pasztorpisti/flashforge-adventurer-3-lid/img/NF-A9x14.png

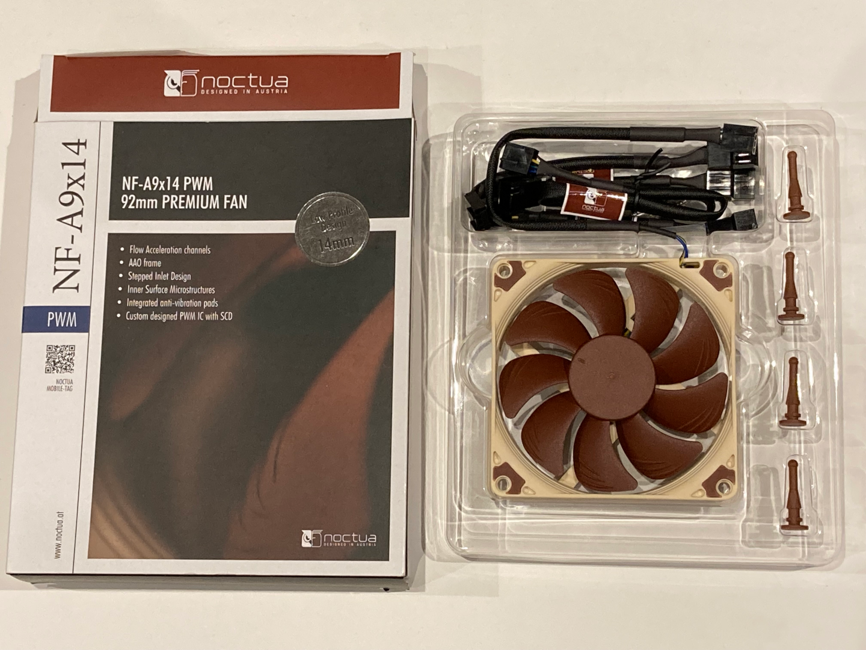
img/NF-A9x14.png
