pasztorpisti/flashforge-adventurer-3-lid/img/NF-A9x14_lid.png

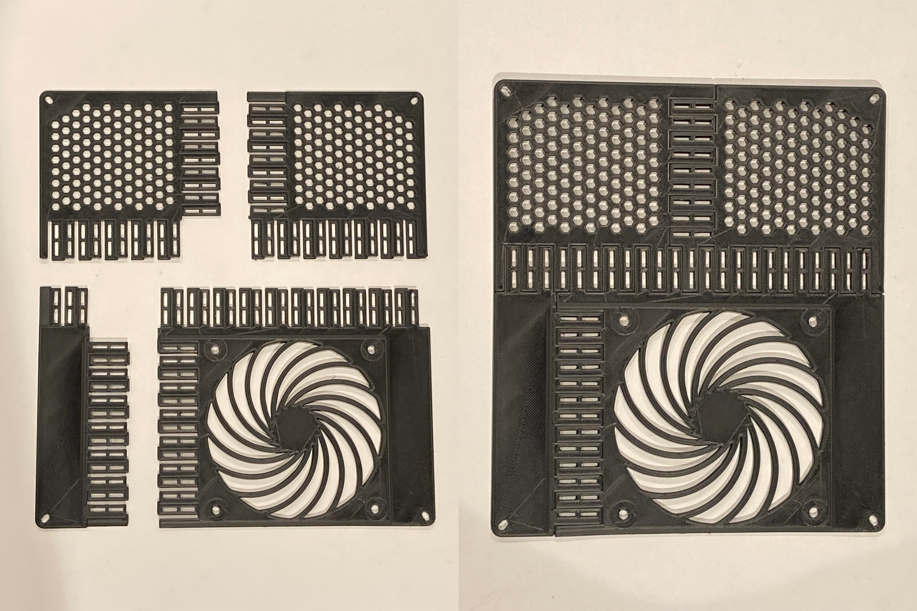
img/NF-A9x14_lid.png
