pasztorpisti/flashforge-adventurer-3-lid/img/NF-A9x14_running.png

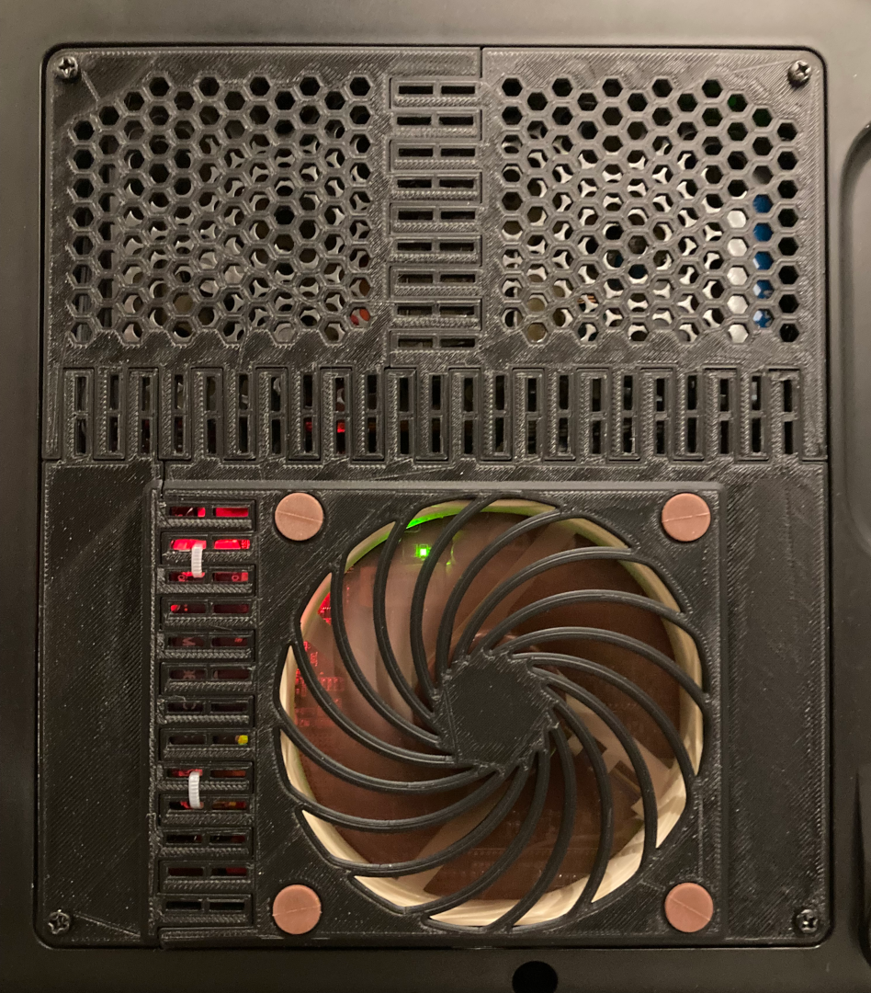
img/NF-A9x14_running.png
