pasztorpisti/flashforge-adventurer-3-lid/img/NF-A9x14_with_buck_converter.png

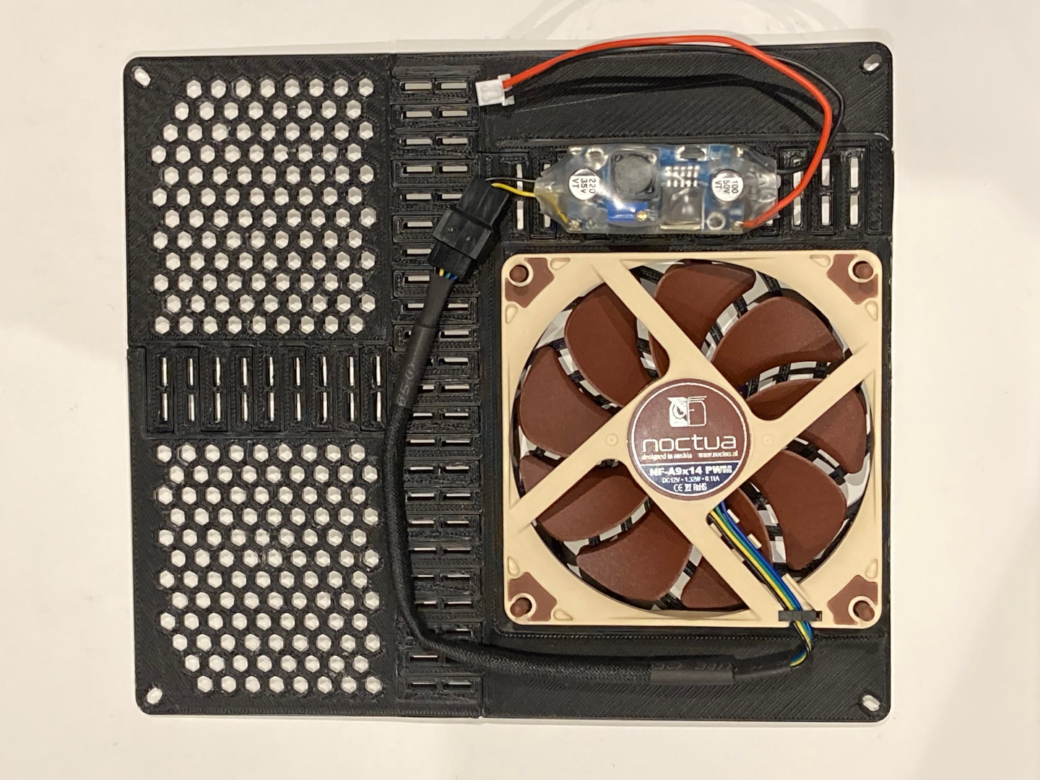
img/NF-A9x14_with_buck_converter.png
