pasztorpisti/flashforge-adventurer-3-lid/stl/lid-92mm/0.18z_0.20xy_lid_top_right.stl

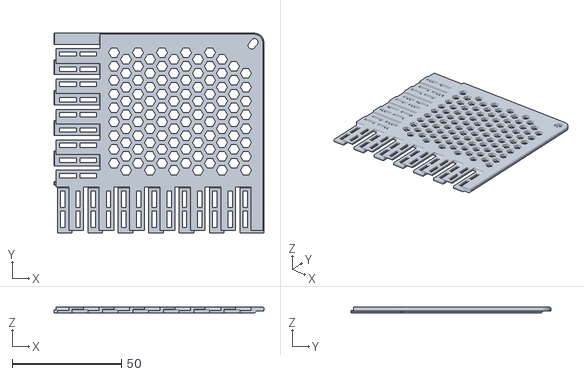
[picture p23: CAD file, 2024-04-19]
stl/lid-92mm/0.18z_0.20xy_lid_top_right.stl
96.0 x 91.3 x 2.88
