pasztorpisti/flashforge-adventurer-3-lid/stl/lid-92mm/0.36z_0.35xy_lid_bottom_left_raised.stl

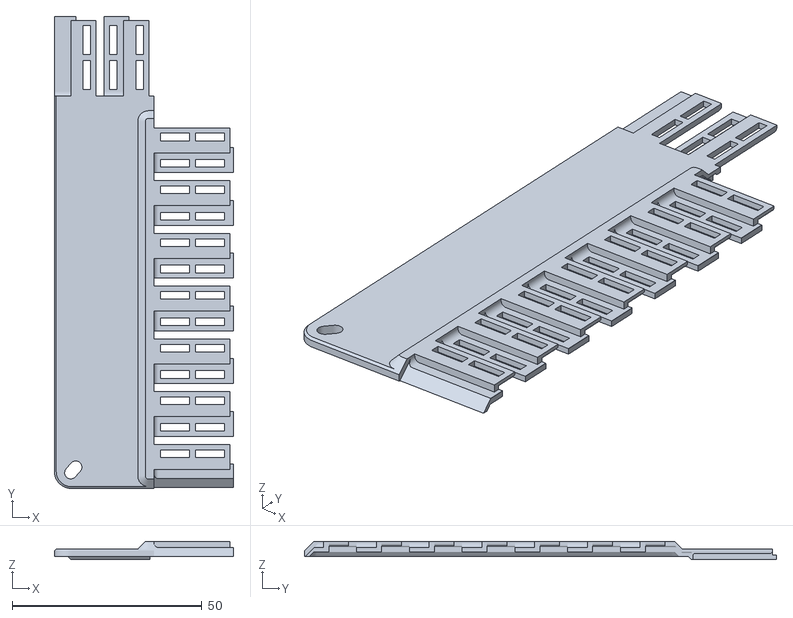
[picture p24: CAD file, 2024-04-19]
stl/lid-92mm/0.36z_0.35xy_lid_bottom_left_raised.stl
47.2 x 124.3 x 4.86
