pasztorpisti/flashforge-adventurer-3-lid/stl/lid-single-part/lid_2x40mm_fans.stl

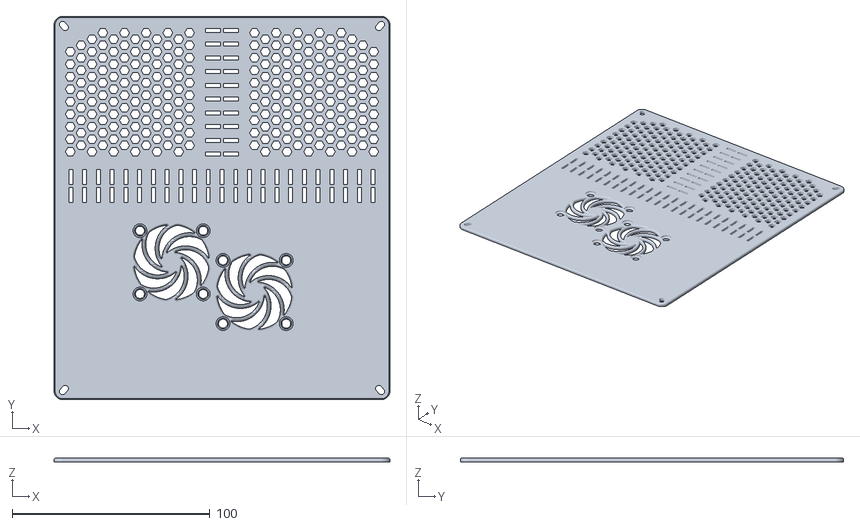
[picture p25: CAD file, 2024-04-19]
stl/lid-single-part/lid_2x40mm_fans.stl
170.0 x 194.0 x 2.00
