pasztorpisti/flashforge-adventurer-3-lid/stl/lid-40mm_or_80mm/0.18z_0.35xy_lid_bottom_left_80mm_fan.stl

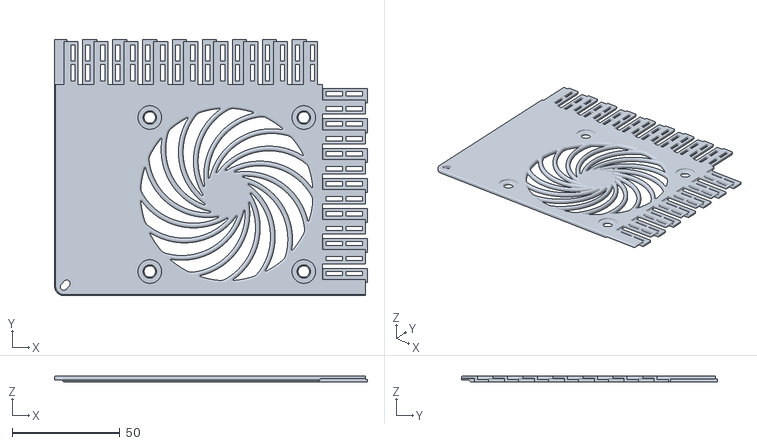
[picture p26: CAD file, 2024-04-19]
stl/lid-40mm_or_80mm/0.18z_0.35xy_lid_bottom_left_80mm_fan.stl
145.3 x 119.1 x 2.88
