pasztorpisti/flashforge-adventurer-3-lid/stl/lid-92mm/0.18z_0.35xy_lid_bottom_left_flat.stl

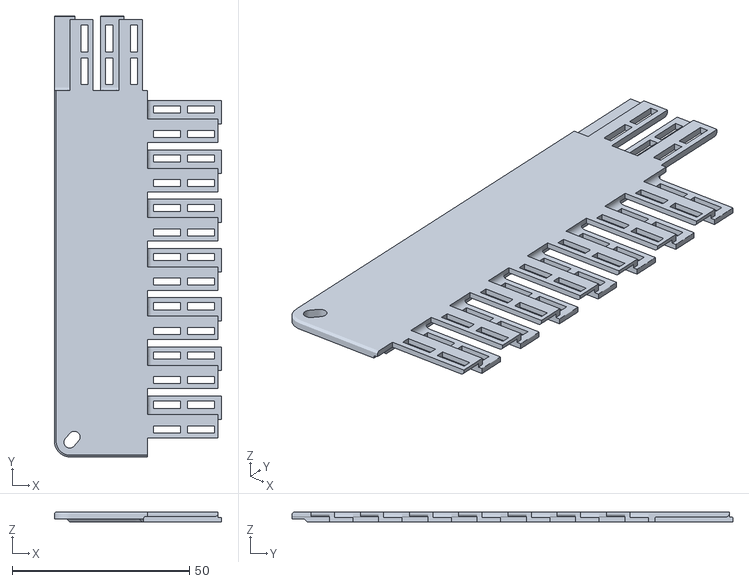
[picture p27: CAD file, 2024-04-19]
stl/lid-92mm/0.18z_0.35xy_lid_bottom_left_flat.stl
47.2 x 124.5 x 2.88
