pasztorpisti/flashforge-adventurer-3-lid/stl/lid-40mm_or_80mm/0.18z_0.30xy_lid_bottom_right.stl

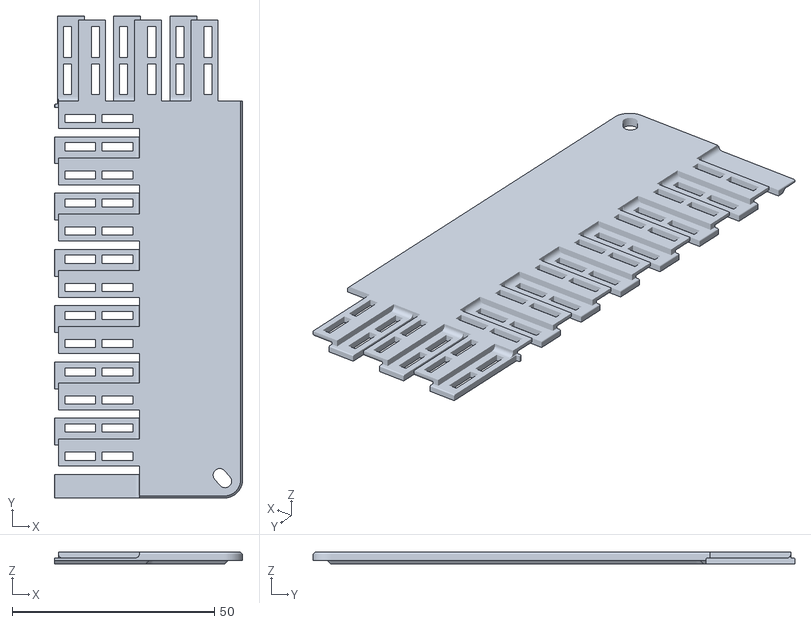
[picture p28: CAD file, 2024-04-19]
stl/lid-40mm_or_80mm/0.18z_0.30xy_lid_bottom_right.stl
46.5 x 119.1 x 2.88
