pasztorpisti/flashforge-adventurer-3-lid/stl/lid-40mm_or_80mm/0.36z_0.25xy_lid_bottom_right.stl

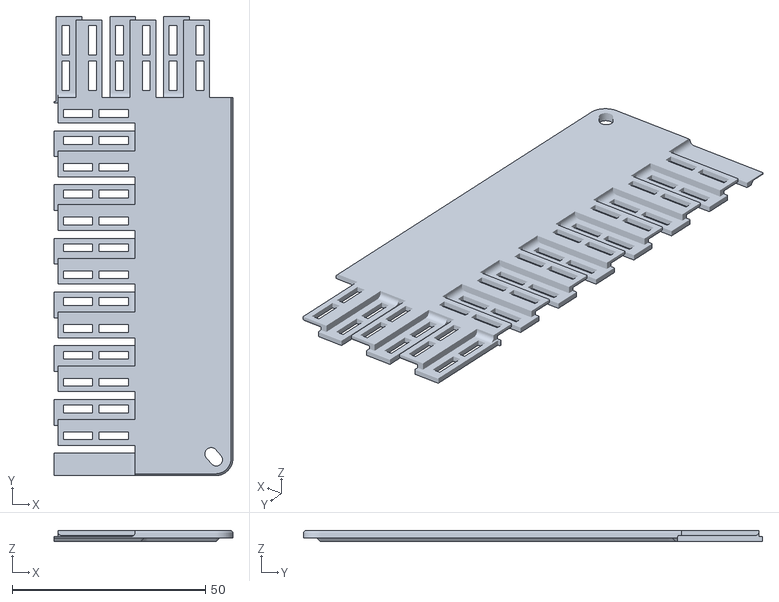
[picture p29: CAD file, 2024-04-19]
stl/lid-40mm_or_80mm/0.36z_0.25xy_lid_bottom_right.stl
46.3 x 118.9 x 2.88
