pasztorpisti/flashforge-adventurer-3-lid/stl/lid-92mm/0.36z_0.15xy_lid_bottom_right_flat.stl

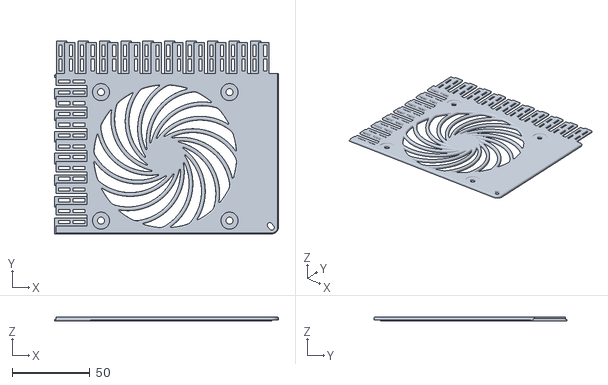
[picture p30: CAD file, 2024-04-19]
stl/lid-92mm/0.36z_0.15xy_lid_bottom_right_flat.stl
144.4 x 124.3 x 2.88
