pasztorpisti/flashforge-adventurer-3-lid/stl/lid-92mm/0.18z_0.25xy_lid_bottom_right_flat.stl

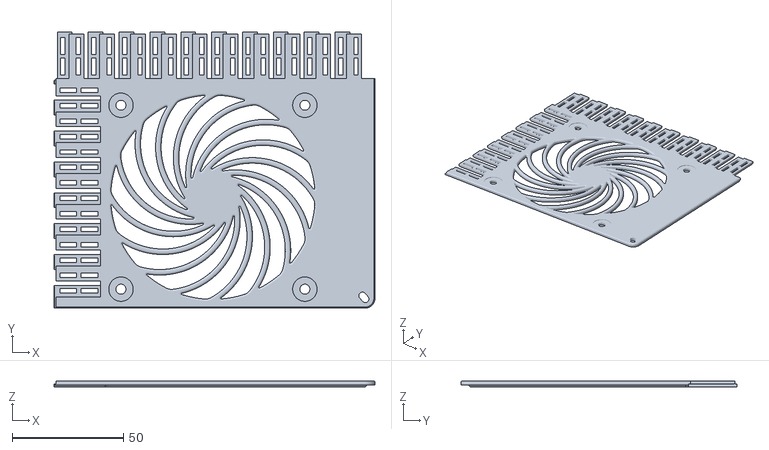
[picture p31: CAD file, 2024-04-19]
stl/lid-92mm/0.18z_0.25xy_lid_bottom_right_flat.stl
144.6 x 124.5 x 2.88
