pasztorpisti/flashforge-adventurer-3-lid/stl/lid-40mm_or_80mm/0.18z_0.20xy_lid_bottom_left_40mm_fans.stl

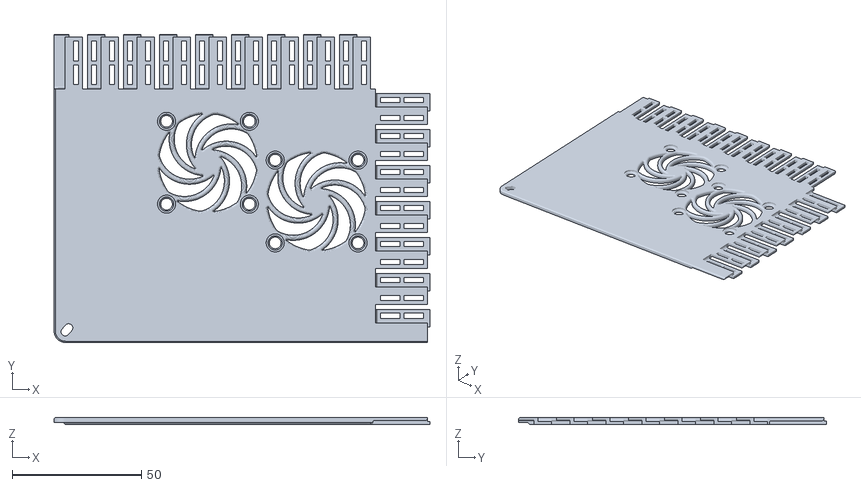
[picture p32: CAD file, 2024-04-19]
stl/lid-40mm_or_80mm/0.18z_0.20xy_lid_bottom_left_40mm_fans.stl
145.3 x 119.1 x 2.88
