pasztorpisti/flashforge-adventurer-3-lid/img/NF-A4x20_and_NF-A4x10_fully_assembled.png

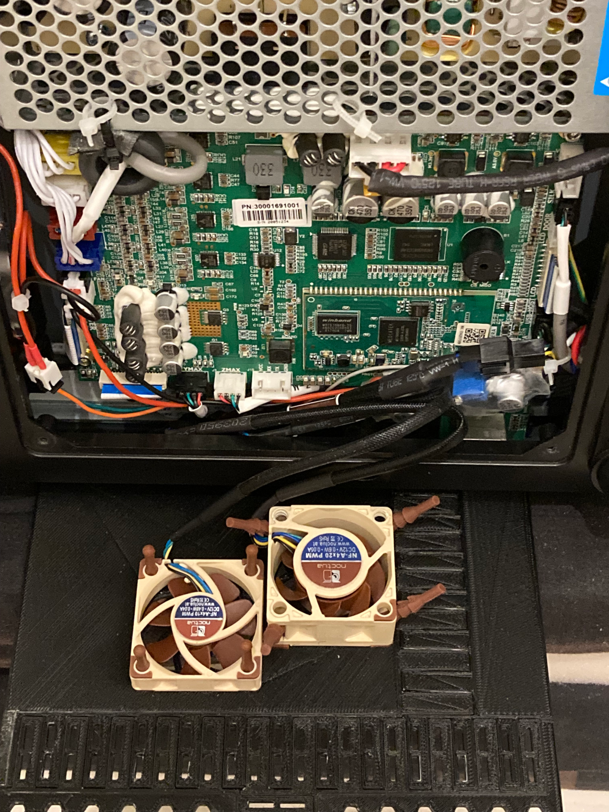
img/NF-A4x20_and_NF-A4x10_fully_assembled.png
